DukeIsCreating/build-a-wheel/cura/CCR10S_FW_PlayerEndSpacer.3mf

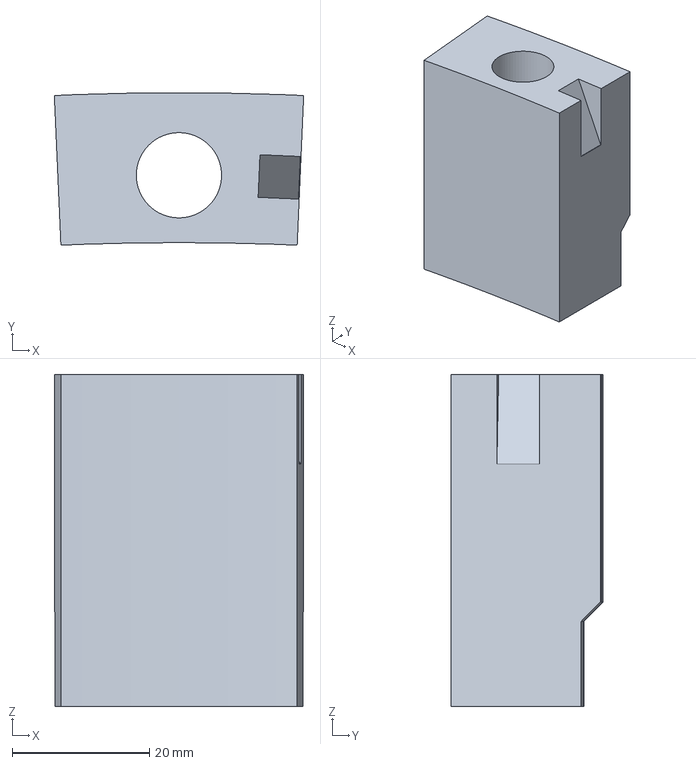
[picture p17: CAD file, 2024-05-18]
cura/CCR10S_FW_PlayerEndSpacer.3mf
36.3 x 22.2 x 48.3 mm
