DukeIsCreating/build-a-wheel/stl/FW_PlayerTop.stl

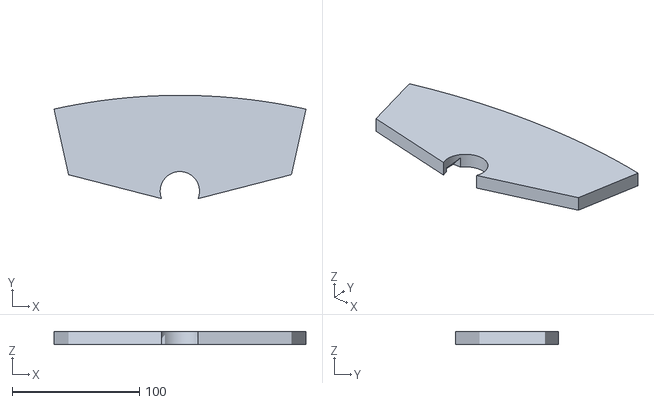
[picture p18: CAD file, 2024-05-18]
stl/FW_PlayerTop.stl
197.7 x 81.1 x 9.90
