DukeIsCreating/build-a-wheel/cura/CCR10S_FW_PlayerSpacer.3mf

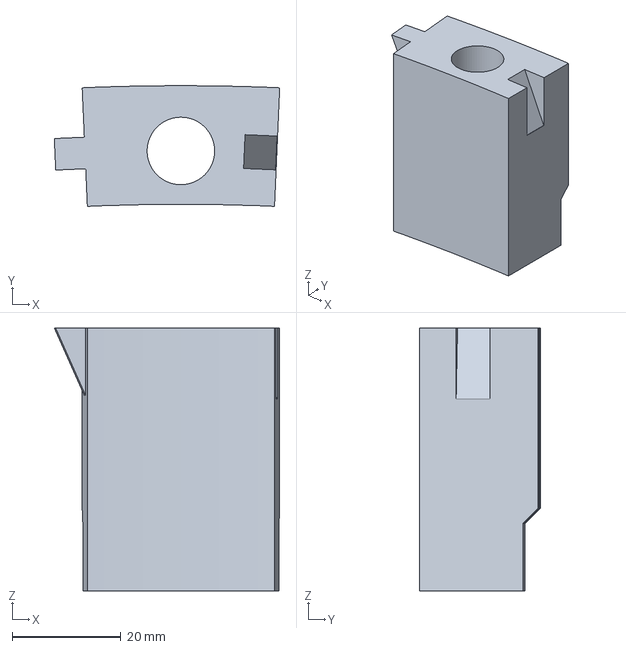
[picture p19: CAD file, 2024-05-18]
cura/CCR10S_FW_PlayerSpacer.3mf
41.4 x 22.2 x 48.3 mm
