DukeIsCreating/build-a-wheel/stl/FW_Rim.stl

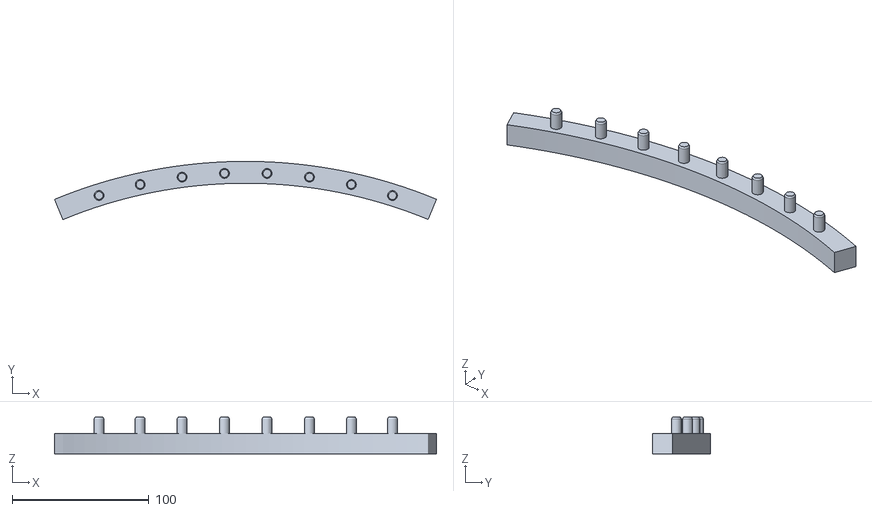
[picture p20: CAD file, 2024-05-18]
stl/FW_Rim.stl
279.5 x 42.6 x 26.9
