DukeIsCreating/build-a-wheel/cura/CCR10S_FW_PtrMed.3mf

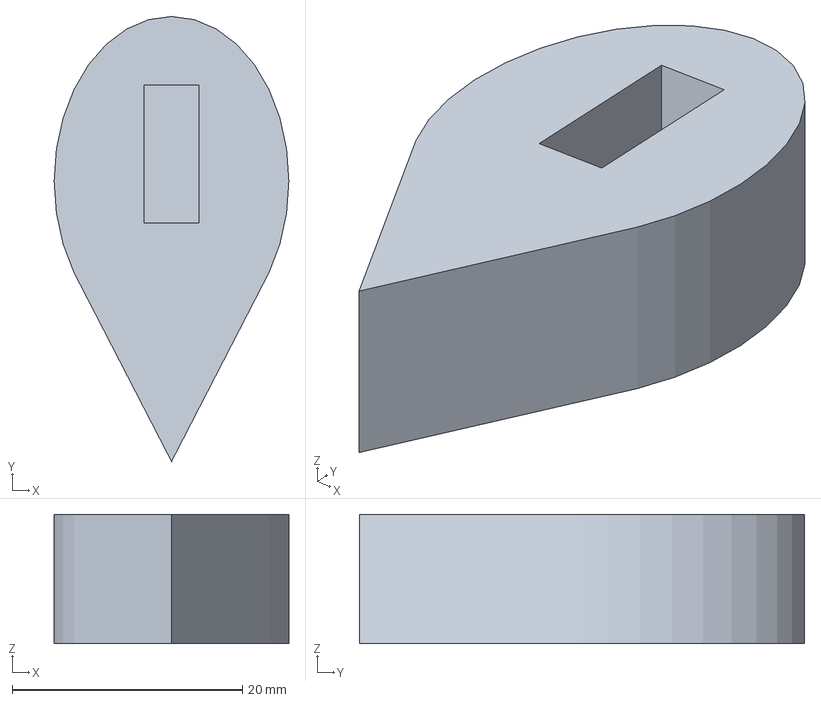
[picture p21: CAD file, 2024-05-18]
cura/CCR10S_FW_PtrMed.3mf
20.4 x 38.7 x 11.2 mm
