DukeIsCreating/build-a-wheel/stl/FW_PtrShaft.stl

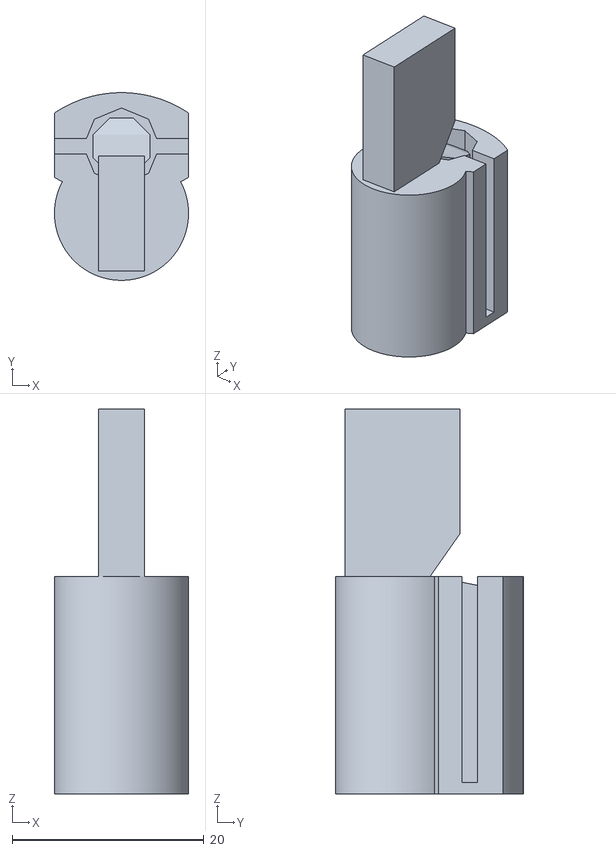
[picture p22: CAD file, 2024-05-18]
stl/FW_PtrShaft.stl
14.0 x 19.6 x 40.2
