DukeIsCreating/build-a-wheel/cura/CCR10S_FW_BaseTop.3mf

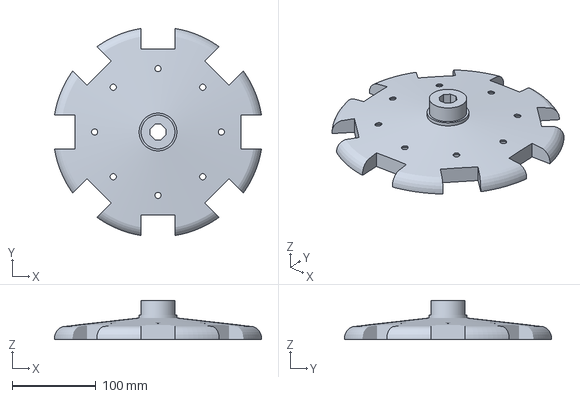
[picture p23: CAD file, 2024-05-18]
cura/CCR10S_FW_BaseTop.3mf
246.6 x 246.6 x 46.5 mm
