DukeIsCreating/build-a-wheel/stl/FW_Support.stl

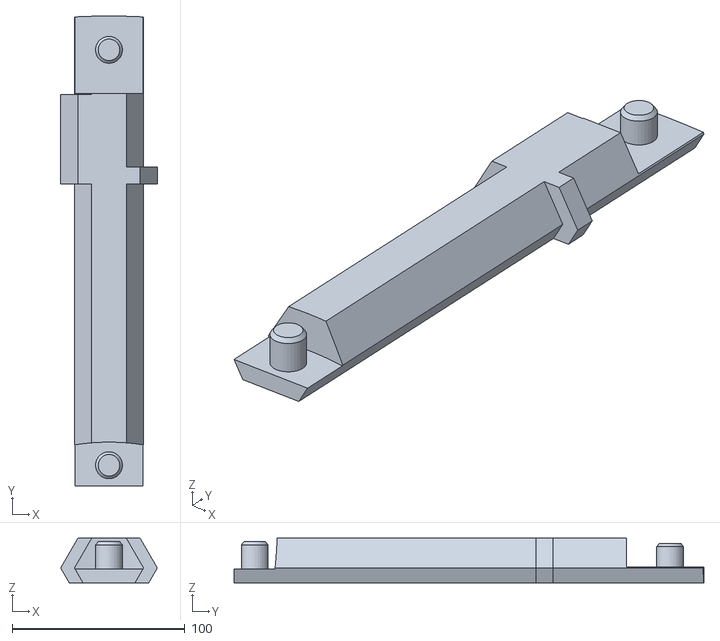
[picture p24: CAD file, 2024-05-18]
stl/FW_Support.stl
56.0 x 272.1 x 26.0
