DukeIsCreating/build-a-wheel/cura/CCR10S_FW_Wedge8Base.3mf

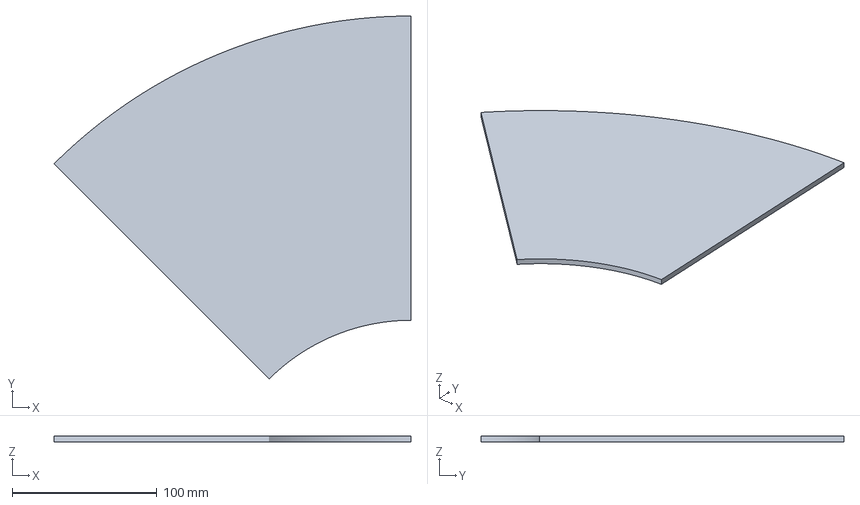
[picture p25: CAD file, 2024-05-18]
cura/CCR10S_FW_Wedge8Base.3mf
246.4 x 250.5 x 3.90 mm
