DukeIsCreating/build-a-wheel/stl/FW_OuterTop.stl

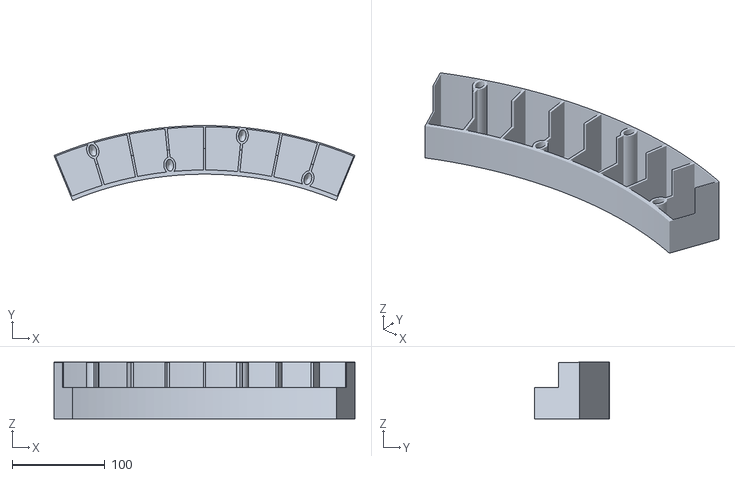
[picture p26: CAD file, 2024-05-18]
stl/FW_OuterTop.stl
325.0 x 80.8 x 61.1
