DukeIsCreating/build-a-wheel/cura/CCR10S_FW_Rim.3mf

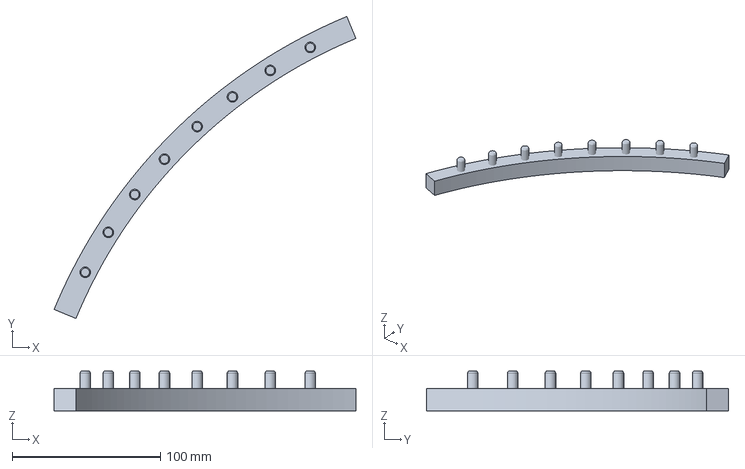
[picture p27: CAD file, 2024-05-18]
cura/CCR10S_FW_Rim.3mf
203.7 x 203.8 x 26.9 mm
