DukeIsCreating/build-a-wheel/stl/FW_WheelC.stl

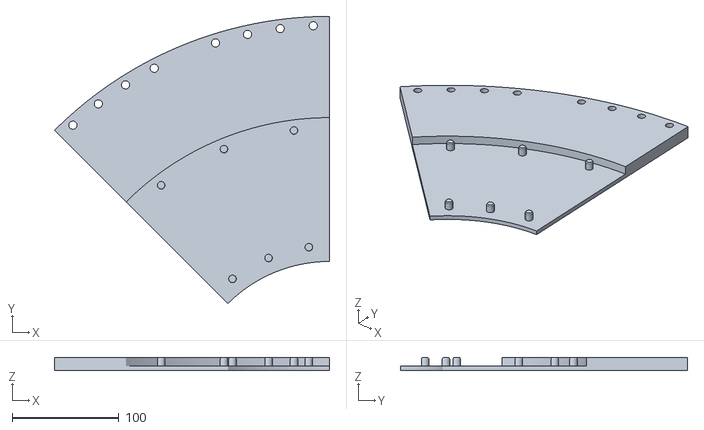
[picture p28: CAD file, 2024-05-18]
stl/FW_WheelC.stl
258.2 x 269.7 x 12.0
