DukeIsCreating/build-a-wheel/cura/CCR10S_FW_OuterTopPlayer.3mf

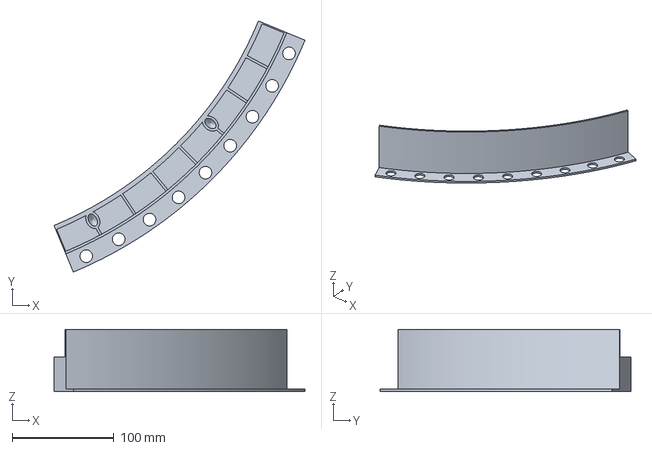
[picture p29: CAD file, 2024-05-18]
cura/CCR10S_FW_OuterTopPlayer.3mf
247.3 x 247.4 x 61.1 mm
