DukeIsCreating/build-a-wheel/stl/FW_Rotor.stl

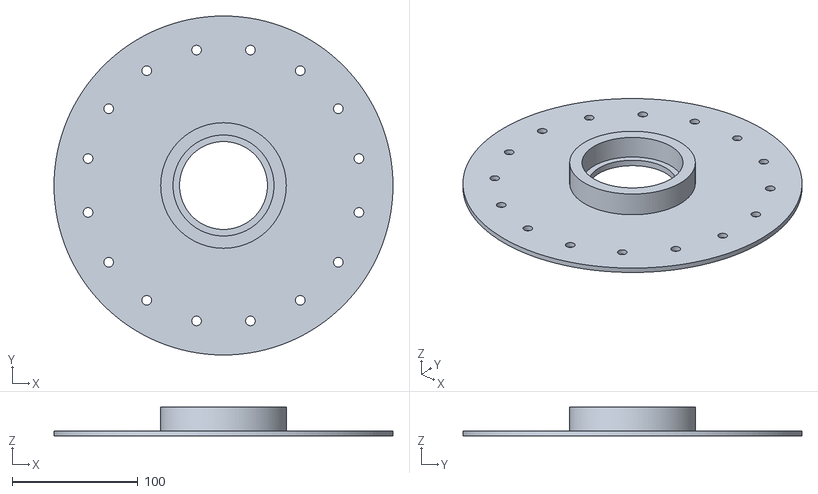
[picture p30: CAD file, 2024-05-18]
stl/FW_Rotor.stl
270.0 x 270.0 x 23.0
