DukeIsCreating/build-a-wheel/cura/CCR10S_FW_MagnetJig.3mf

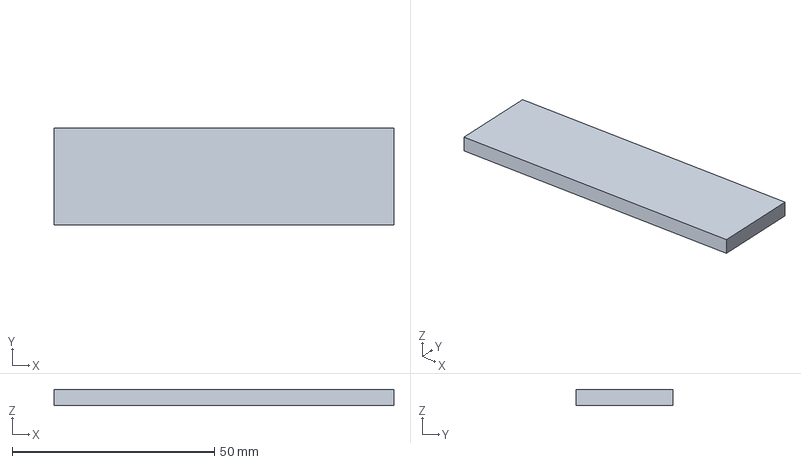
[picture p31: CAD file, 2024-05-18]
cura/CCR10S_FW_MagnetJig.3mf
84.0 x 24.0 x 4.00 mm
