DukeIsCreating/build-a-wheel/stl/FW_PlayerMount.stl

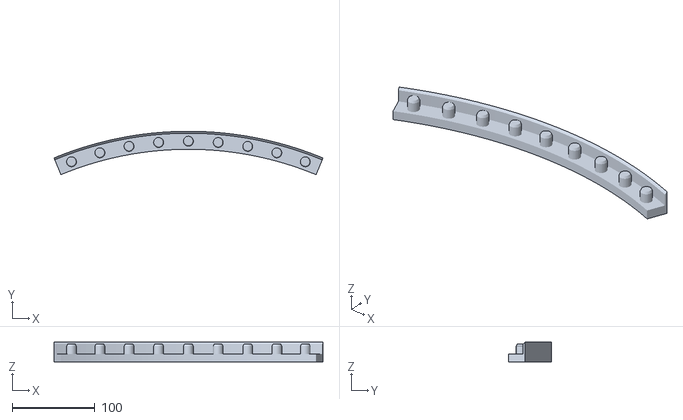
[picture p32: CAD file, 2024-05-18]
stl/FW_PlayerMount.stl
325.0 x 52.5 x 23.8
