DukeIsCreating/build-a-wheel/cura/CCR10S_FW_2x_AddWedge24Base.3mf

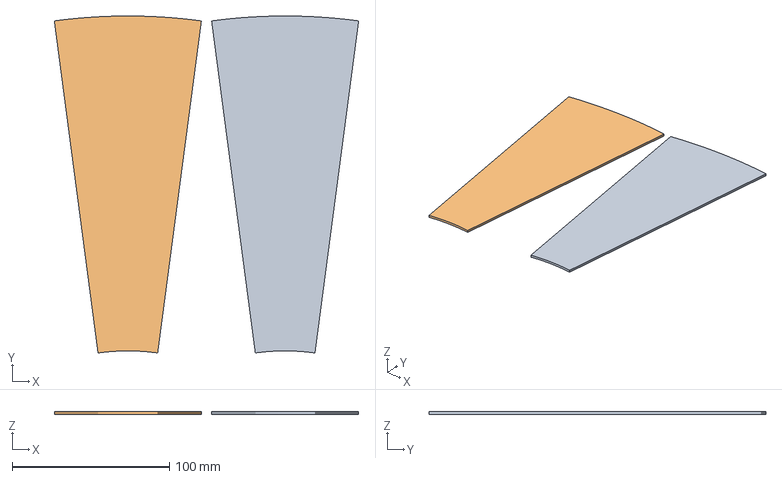
[picture p33: CAD file, 2024-05-18]
cura/CCR10S_FW_2x_AddWedge24Base.3mf
193.5 x 214.3 x 1.75 mm
FW_WedgeOvr.stl
FW_WedgeOvr.stl(1)
