DukeIsCreating/build-a-wheel/cura/CCR10S_FW_BaseBottom.3mf

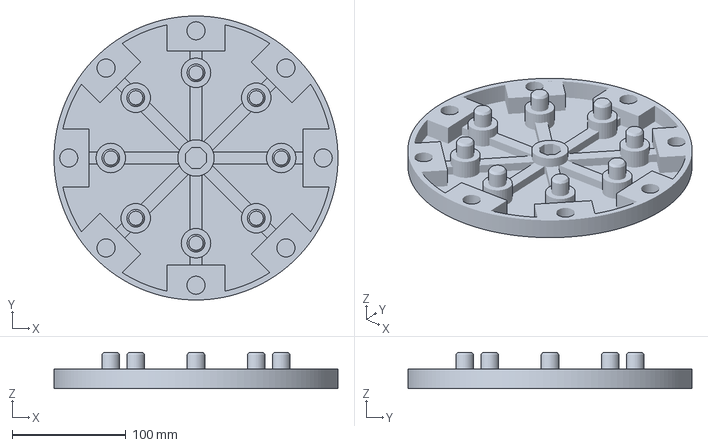
[picture p34: CAD file, 2024-05-18]
cura/CCR10S_FW_BaseBottom.3mf
250.0 x 250.0 x 32.0 mm
