DukeIsCreating/build-a-wheel/stl/FW_PlayerBtm.stl

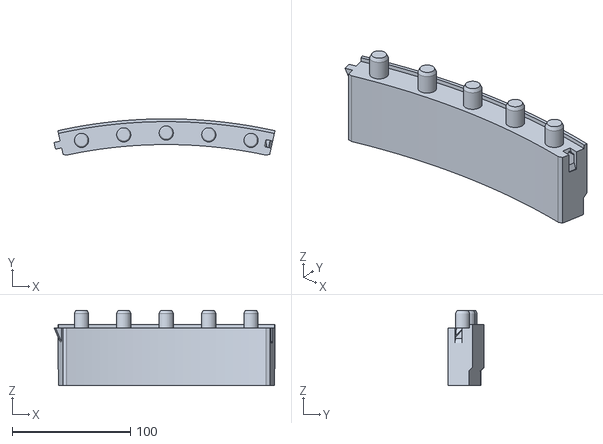
[picture p35: CAD file, 2024-05-18]
stl/FW_PlayerBtm.stl
187.0 x 30.8 x 63.6
