DukeIsCreating/build-a-wheel/stl/FW_OuterTopPlayer.stl

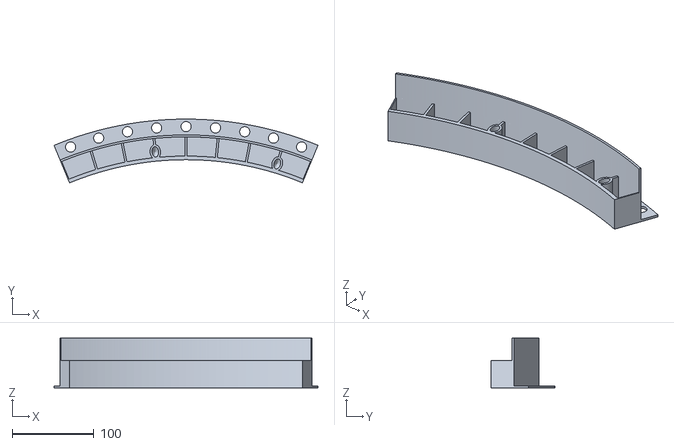
[picture p36: CAD file, 2024-05-18]
stl/FW_OuterTopPlayer.stl
322.9 x 78.1 x 61.1
