DukeIsCreating/build-a-wheel/cura/CCR10S_FW_Support.3mf

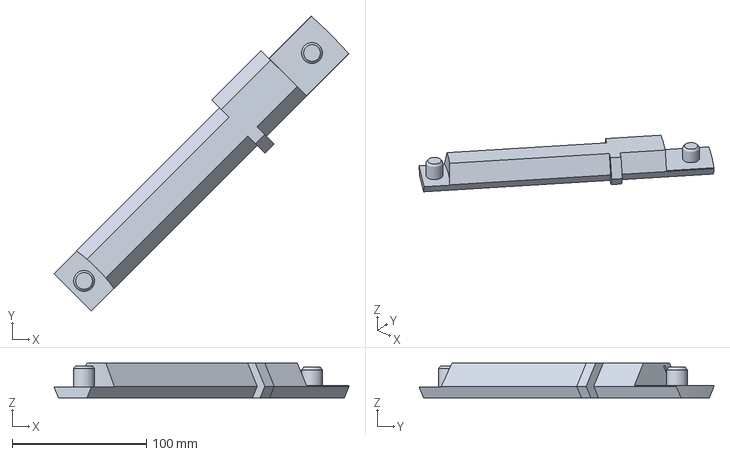
[picture p37: CAD file, 2024-05-18]
cura/CCR10S_FW_Support.3mf
220.1 x 220.1 x 26.0 mm
